wesrchow/Automated-Robotic-Sorting-Arm/Machine_learning/IMG_2049.jpg

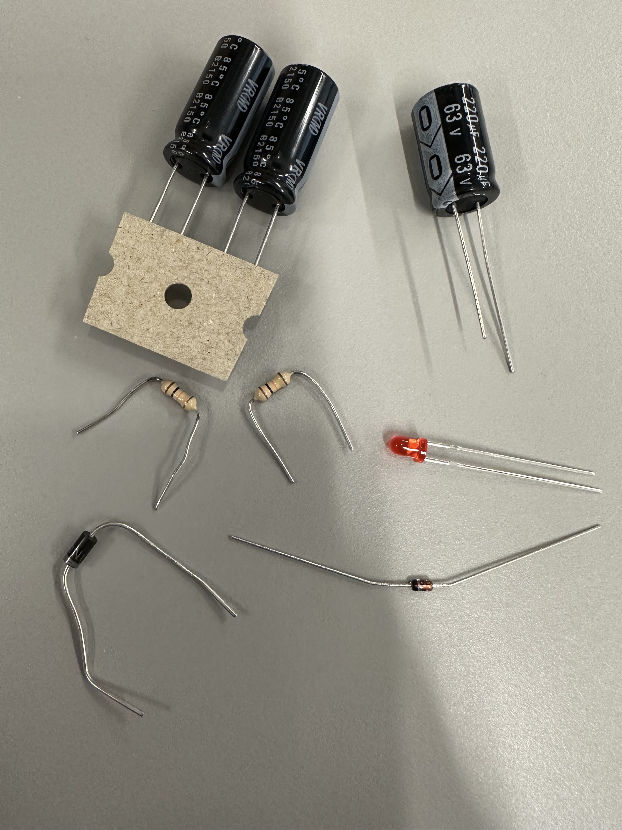
Machine_learning/IMG_2049.jpg
