wesrchow/Automated-Robotic-Sorting-Arm/Main/detection.jpg

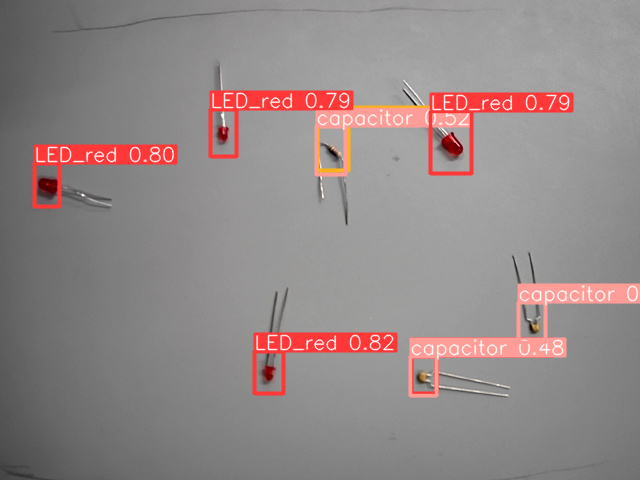
Main/detection.jpg
