wesrchow/Automated-Robotic-Sorting-Arm/ML_dataset/train/images/WIN_20230320_16_11_41_Pro_jpg.rf.b69abedbc1ccda08bdd52ff2d2267f6c.jpg

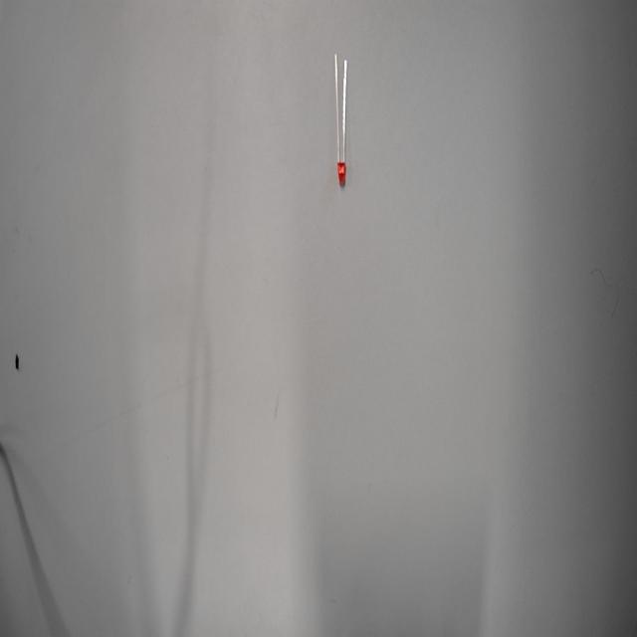
ML_dataset/train/images/WIN_20230320_16_11_41_Pro_jpg.rf.b69abedbc1ccda08bdd52ff2d2267f6c.jpg
