wesrchow/Automated-Robotic-Sorting-Arm/ML_dataset/train/images/WIN_20230320_16_13_38_Pro_jpg.rf.ac4fd47913d84867d70a505b9c8567f9.jpg

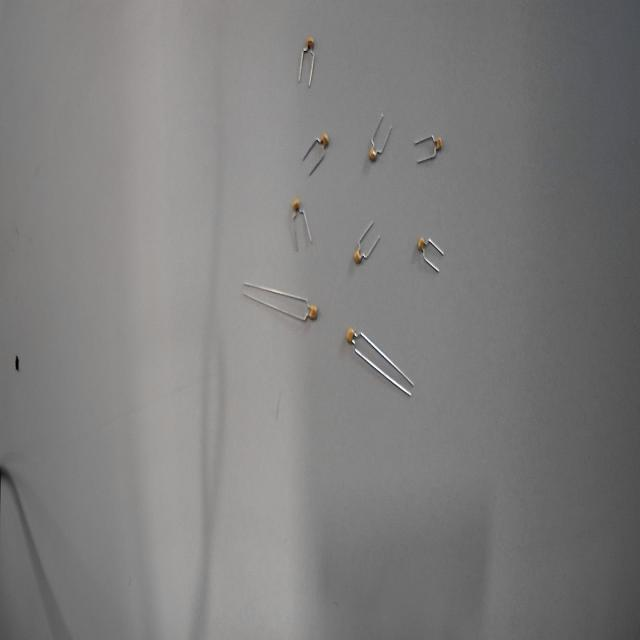
ML_dataset/train/images/WIN_20230320_16_13_38_Pro_jpg.rf.ac4fd47913d84867d70a505b9c8567f9.jpg
