wesrchow/Automated-Robotic-Sorting-Arm/ML_dataset/train/images/WIN_20230320_16_13_49_Pro_jpg.rf.a0906ef544d4f4db993aecd556fcd15e.jpg

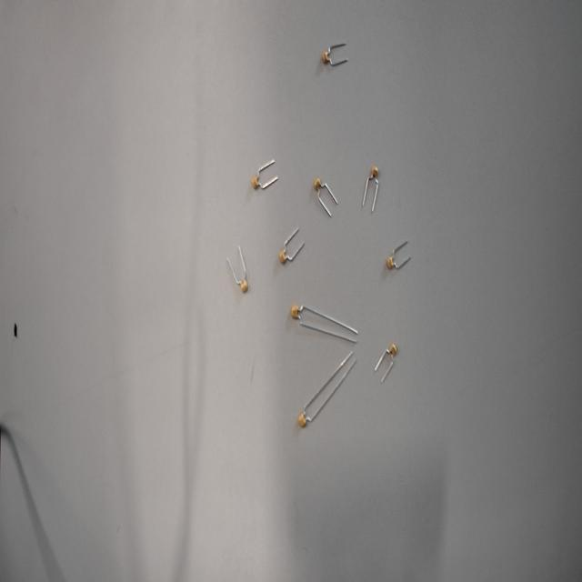
ML_dataset/train/images/WIN_20230320_16_13_49_Pro_jpg.rf.a0906ef544d4f4db993aecd556fcd15e.jpg
