wesrchow/Automated-Robotic-Sorting-Arm/ML_dataset/train/images/WIN_20230320_16_16_34_Pro_jpg.rf.e743581d52dabc2f4080c80f24b02915.jpg

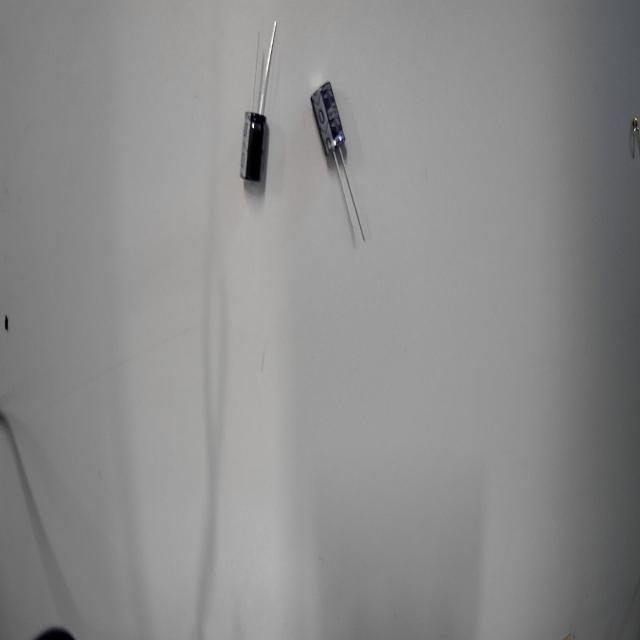
ML_dataset/train/images/WIN_20230320_16_16_34_Pro_jpg.rf.e743581d52dabc2f4080c80f24b02915.jpg
