wesrchow/Automated-Robotic-Sorting-Arm/ML_dataset/train/images/WIN_20230320_16_16_49_Pro_jpg.rf.842495ae2638b46b3d1597df2e734d61.jpg

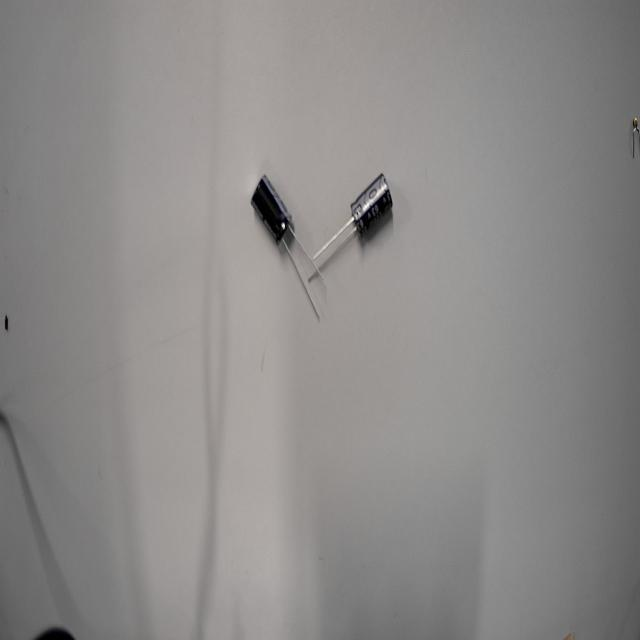
ML_dataset/train/images/WIN_20230320_16_16_49_Pro_jpg.rf.842495ae2638b46b3d1597df2e734d61.jpg
