wesrchow/Automated-Robotic-Sorting-Arm/ML_dataset/train/images/WIN_20230320_16_17_00_Pro_jpg.rf.023a3cab5698b078e2380215b9ef5a75.jpg

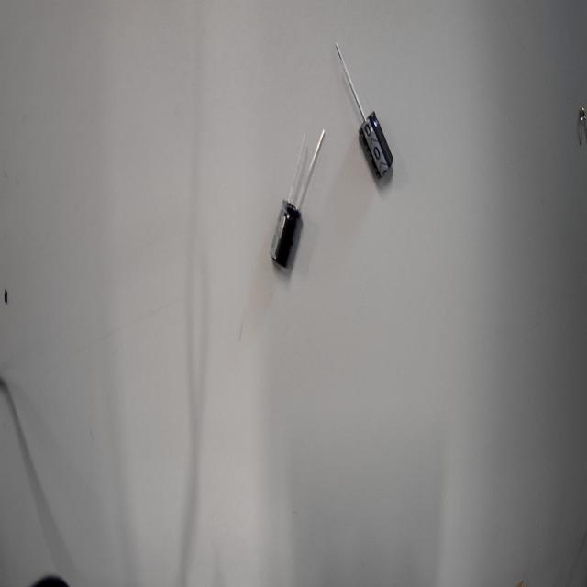
ML_dataset/train/images/WIN_20230320_16_17_00_Pro_jpg.rf.023a3cab5698b078e2380215b9ef5a75.jpg
