wesrchow/Automated-Robotic-Sorting-Arm/ML_dataset/train/images/WIN_20230320_16_20_28_Pro_jpg.rf.11ab117baa12f461b413f4ab6f04bc1d.jpg

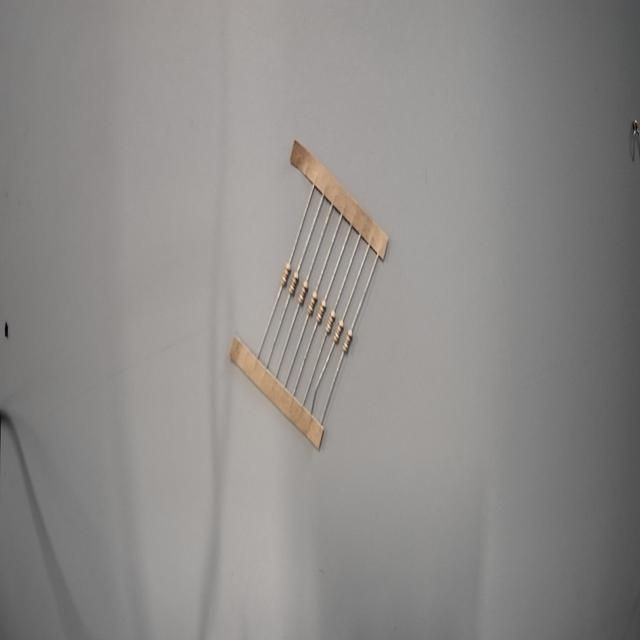
ML_dataset/train/images/WIN_20230320_16_20_28_Pro_jpg.rf.11ab117baa12f461b413f4ab6f04bc1d.jpg
