wesrchow/Automated-Robotic-Sorting-Arm/ML_dataset/train/images/WIN_20230320_16_22_34_Pro_jpg.rf.9bb959c5d1f27a96867d862136e7fbc3.jpg

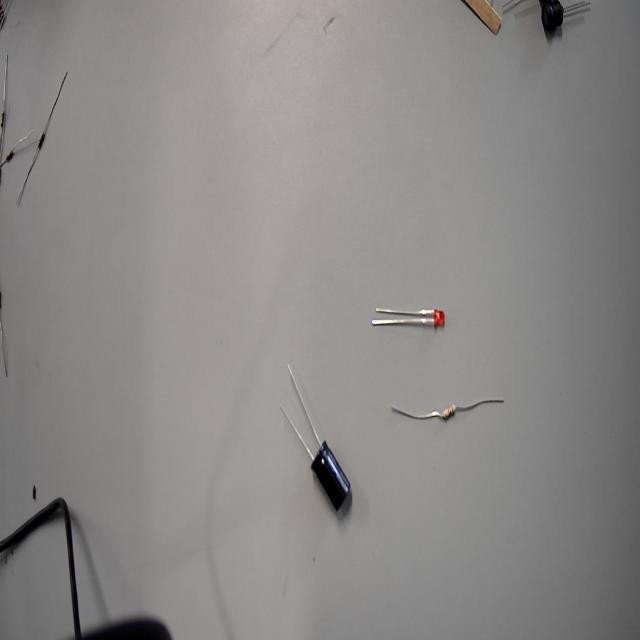
ML_dataset/train/images/WIN_20230320_16_22_34_Pro_jpg.rf.9bb959c5d1f27a96867d862136e7fbc3.jpg
