wesrchow/Automated-Robotic-Sorting-Arm/ML_dataset/train/images/WIN_20230404_08_58_23_Pro_jpg.rf.4651e8e9c125e11d67ce9b2da522ae1c.jpg

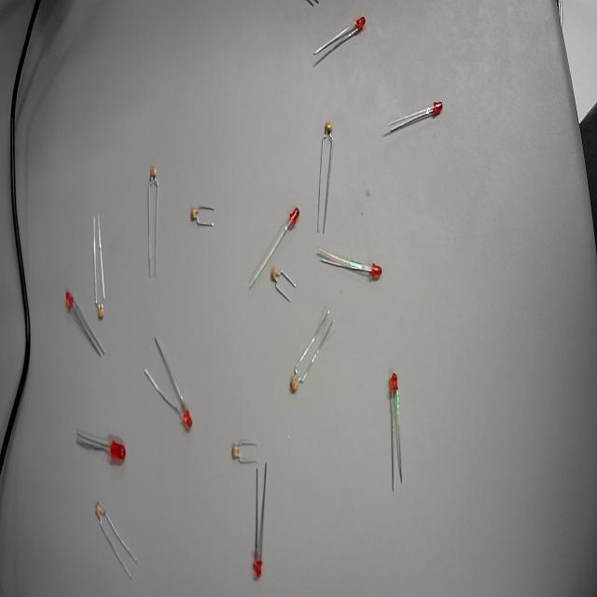
ML_dataset/train/images/WIN_20230404_08_58_23_Pro_jpg.rf.4651e8e9c125e11d67ce9b2da522ae1c.jpg
