wesrchow/Automated-Robotic-Sorting-Arm/ML_dataset/train/images/WIN_20230404_08_59_55_Pro_jpg.rf.8511e575d8cd6d93aa103133a889b3f5.jpg

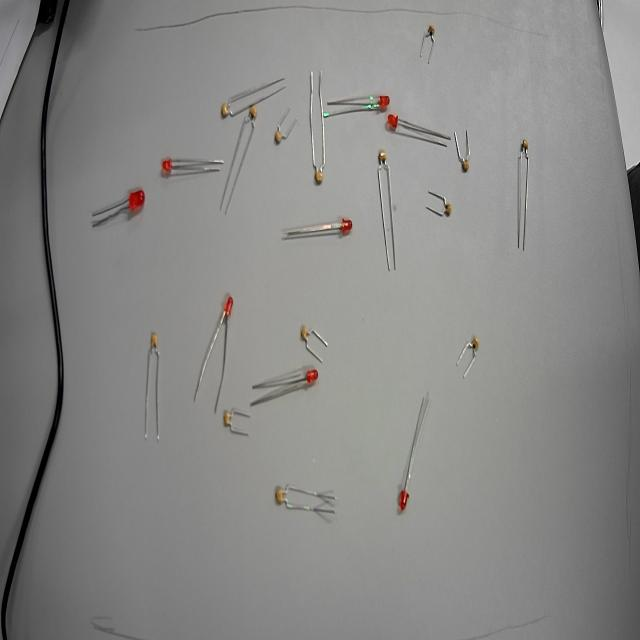
ML_dataset/train/images/WIN_20230404_08_59_55_Pro_jpg.rf.8511e575d8cd6d93aa103133a889b3f5.jpg
