wesrchow/Automated-Robotic-Sorting-Arm/ML_dataset/train/images/WIN_20230404_09_00_06_Pro_jpg.rf.62b5fa4198184a26cc7e2f2a9ac3aab7.jpg

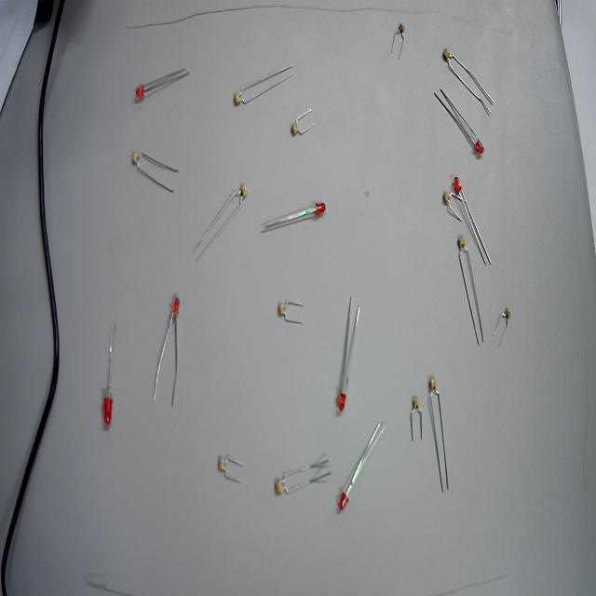
ML_dataset/train/images/WIN_20230404_09_00_06_Pro_jpg.rf.62b5fa4198184a26cc7e2f2a9ac3aab7.jpg
