wesrchow/Automated-Robotic-Sorting-Arm/ML_dataset/train/images/WIN_20230404_09_00_49_Pro_jpg.rf.cd7cd0c49d260988451196a729dc4bad.jpg

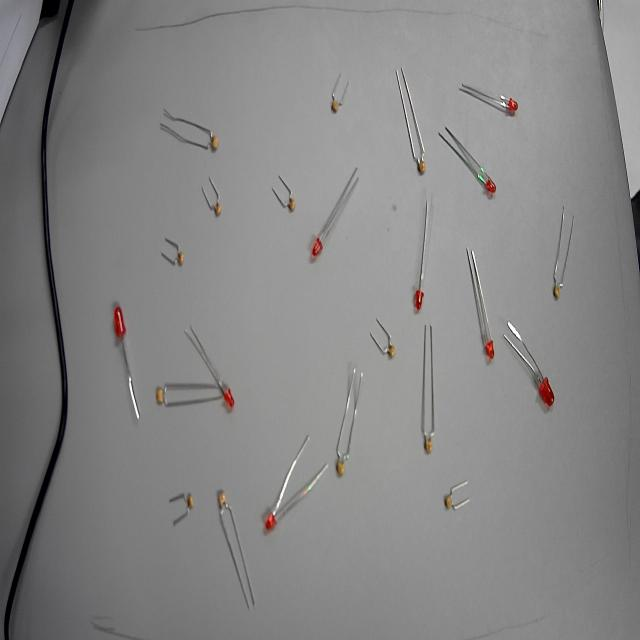
ML_dataset/train/images/WIN_20230404_09_00_49_Pro_jpg.rf.cd7cd0c49d260988451196a729dc4bad.jpg
