wesrchow/Automated-Robotic-Sorting-Arm/ML_dataset/train/images/WIN_20230404_09_05_30_Pro_jpg.rf.b21ef2a2d349b299af1ea2f8e37cad5c.jpg

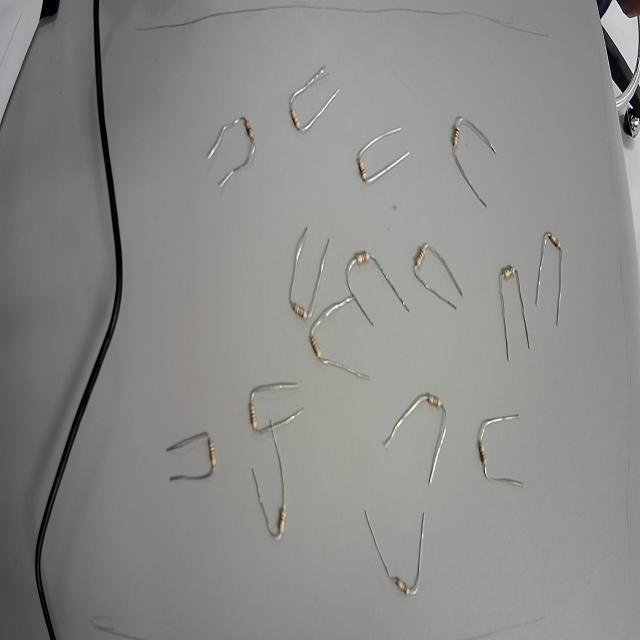
ML_dataset/train/images/WIN_20230404_09_05_30_Pro_jpg.rf.b21ef2a2d349b299af1ea2f8e37cad5c.jpg
