wesrchow/Automated-Robotic-Sorting-Arm/ML_dataset/valid/images/WIN_20230320_16_12_24_Pro_jpg.rf.549e07704ee7566cf660213aab729224.jpg

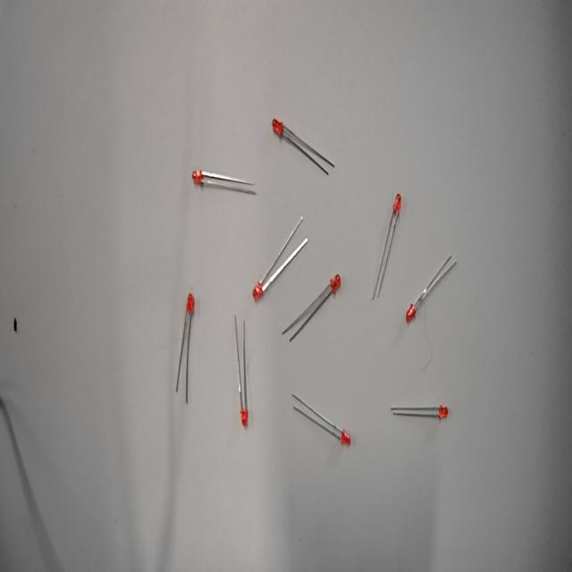
ML_dataset/valid/images/WIN_20230320_16_12_24_Pro_jpg.rf.549e07704ee7566cf660213aab729224.jpg
