wesrchow/Automated-Robotic-Sorting-Arm/ML_dataset/valid/images/WIN_20230320_16_20_24_Pro_jpg.rf.a1bb5adee2957037d93624c651f2d64c.jpg

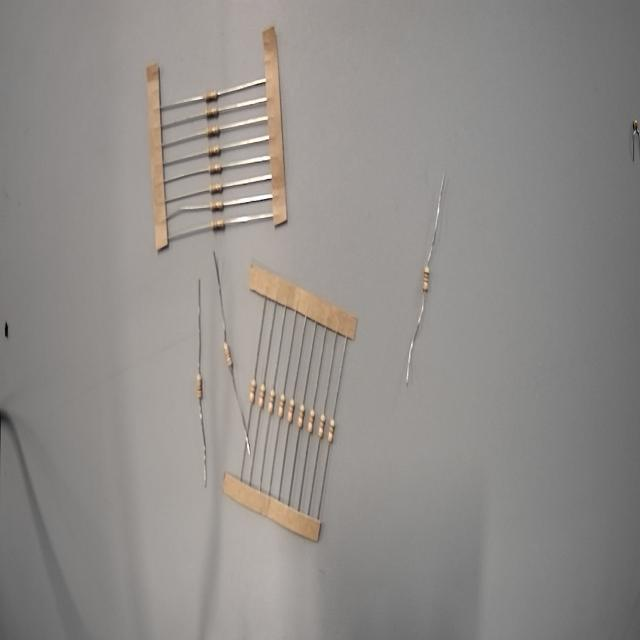
ML_dataset/valid/images/WIN_20230320_16_20_24_Pro_jpg.rf.a1bb5adee2957037d93624c651f2d64c.jpg
