wesrchow/Automated-Robotic-Sorting-Arm/ML_dataset/test/images/WIN_20230320_16_16_39_Pro_jpg.rf.208555584290748ef8a520ba1338cb12.jpg

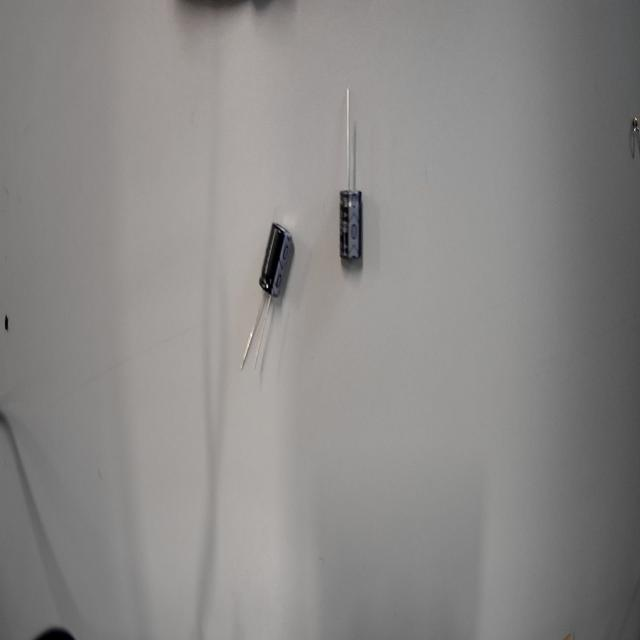
ML_dataset/test/images/WIN_20230320_16_16_39_Pro_jpg.rf.208555584290748ef8a520ba1338cb12.jpg
