wesrchow/Automated-Robotic-Sorting-Arm/ML_dataset/test/images/WIN_20230404_09_04_30_Pro_jpg.rf.67095489e8c483c81b6eb0461b97e991.jpg

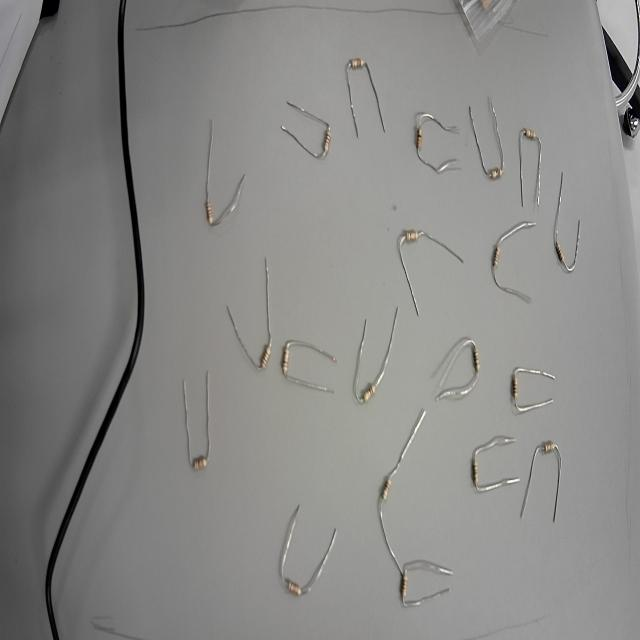
ML_dataset/test/images/WIN_20230404_09_04_30_Pro_jpg.rf.67095489e8c483c81b6eb0461b97e991.jpg
